Rainer-G/Gas_Meter/Gas_Meter/include/Gas_Time.h

// Time routines for Gas Logger
//
// Time routines for GAS Counter
//
//
//
#include "time.h"

struct txx                         // just for a reminder of data available
{
  int tm_sec;
  int tm_min;
  int tm_hour;
  int tm_mday;
  int tm_mon;
  int tm_year;
  int tm_wday;
  int tm_yday;
  int tm_isdst;
#ifdef __TM_GMTOFF
  long  __TM_GMTOFF;
#endif
#ifdef __TM_ZONE
  const char *__TM_ZONE;
#endif
};


const char* ntpServer          = "pool.ntp.org";
const long  gmtOffset_sec      = 3600;
const int   daylightOffset_sec = 3600;
int         Gas_hour;
int         Gas_min;
int         Gas_sec;
int         Gas_month;
int         Gas_day;
int         Gas_year;

//
//
//***********************************************************************************************
//
//  time routines
//
//**********************************************************************************************
//
void get_LocalTime()
{
  struct tm timeinfo;
  
 // 
  if (WiFi.status() != WL_CONNECTED)
  {
    Gas_WiFi_reconnect();
  }
//
  if( !getLocalTime( &timeinfo ) )
  {
//    logprint( "\r\nFailed to obtain time\r\n" );
    return;
  }
  Gas_hour  = timeinfo.tm_hour;
  Gas_min   = timeinfo.tm_min;
  Gas_sec   = timeinfo.tm_sec;
  Gas_day   = timeinfo.tm_mday;
  Gas_month = timeinfo.tm_mon  + 1;
  Gas_year  = timeinfo.tm_year + 1900;
  
}


void begin_time()
{
  //init and get the time
  configTime( gmtOffset_sec, daylightOffset_sec, ntpServer );
  get_LocalTime();
 
}
